teodora-voicu/Proiect_TSC/Images/display.png

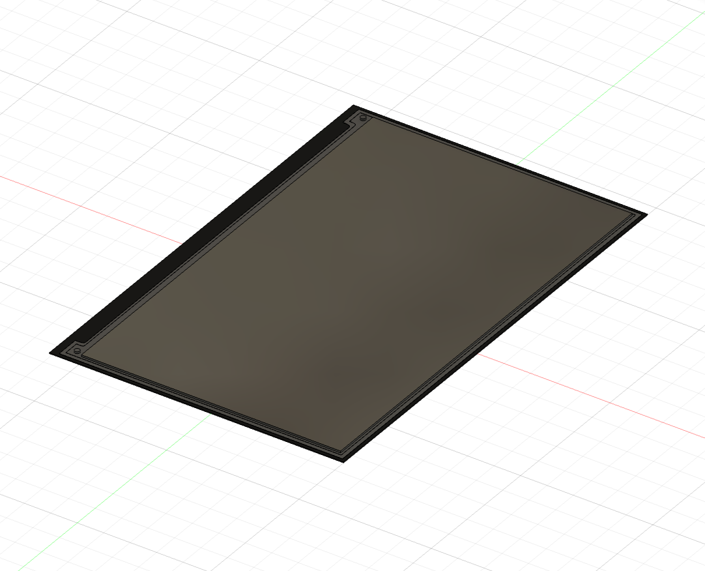
Images/display.png
